rmckay/sgu10adapters/imgs/IMG_20190721_045112.jpg

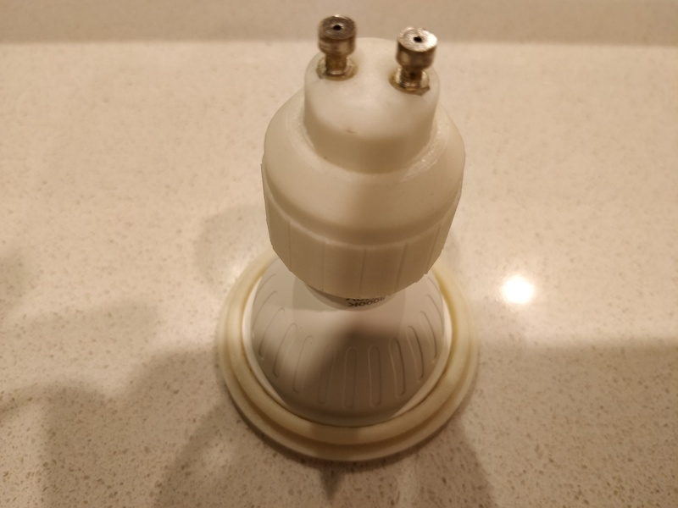
imgs/IMG_20190721_045112.jpg
