rmckay/sgu10adapters/imgs/IMG_20190721_045136.jpg

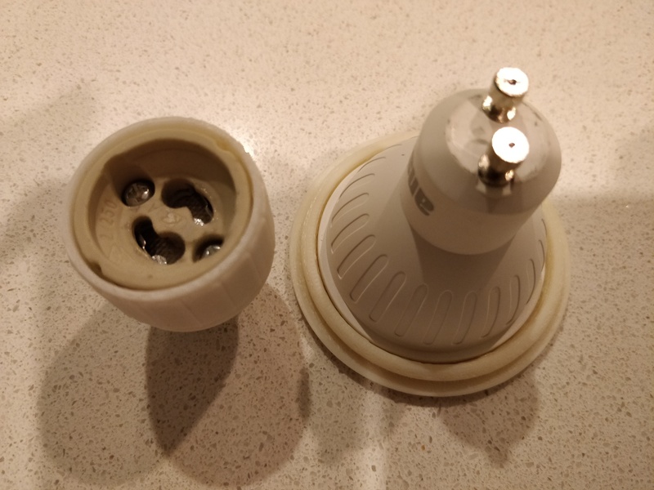
imgs/IMG_20190721_045136.jpg
