rmckay/sgu10adapters/imgs/IMG_20190721_045154.jpg

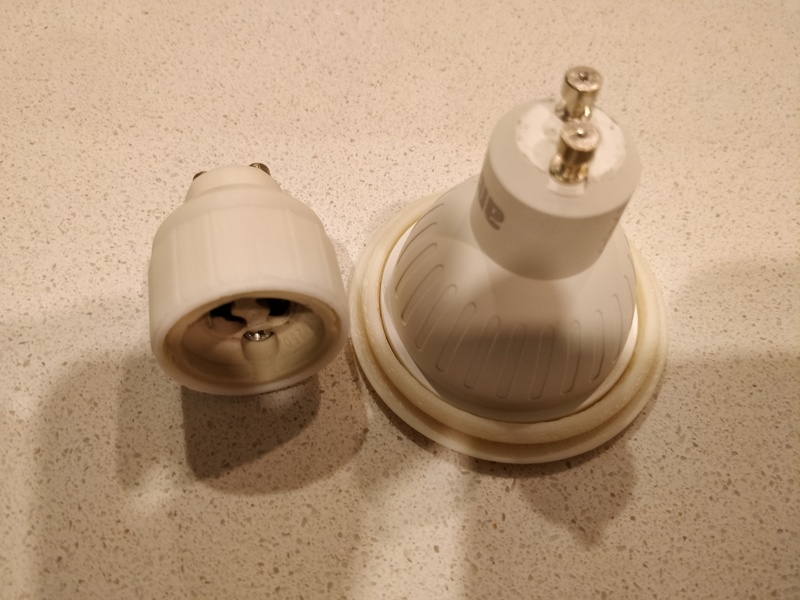
imgs/IMG_20190721_045154.jpg
